16n-faderbank/16n/build/build/16n_1.jpg

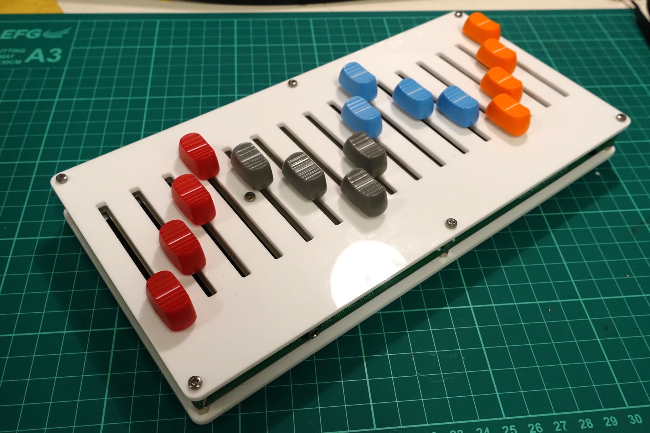
build/build/16n_1.jpg
