16n-faderbank/16n/build/build/16n_1_ics.png

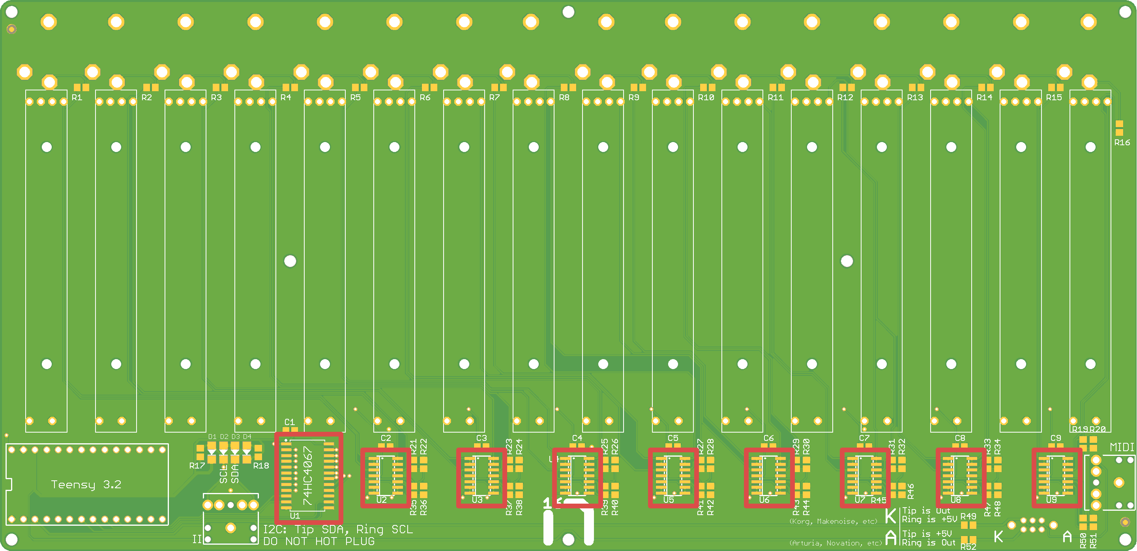
build/build/16n_1_ics.png
