16n-faderbank/16n/build/build/16n_2_rcs.png

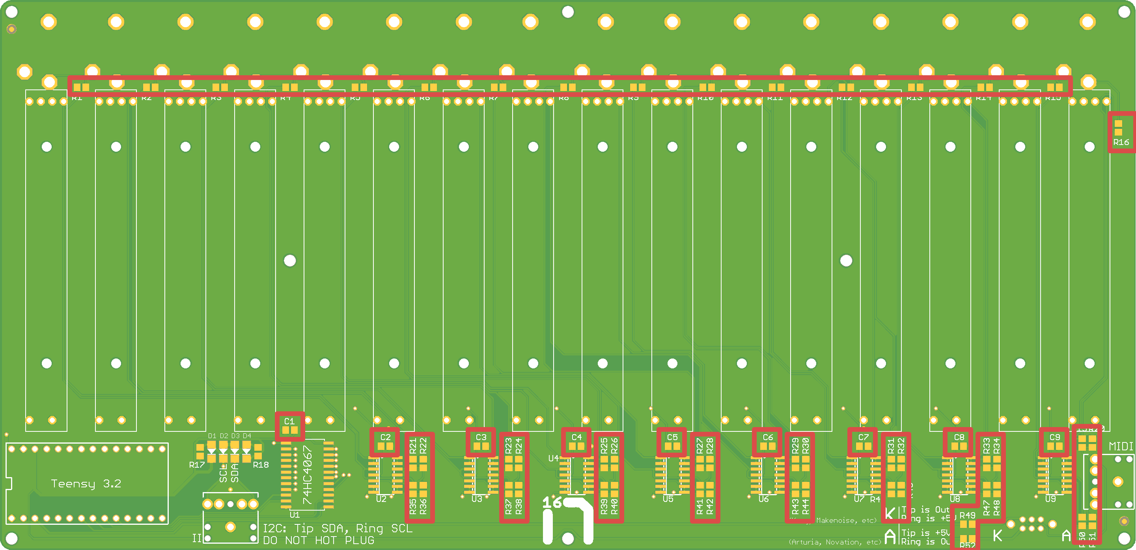
build/build/16n_2_rcs.png
