16n-faderbank/16n/build/build/16n_3.jpg

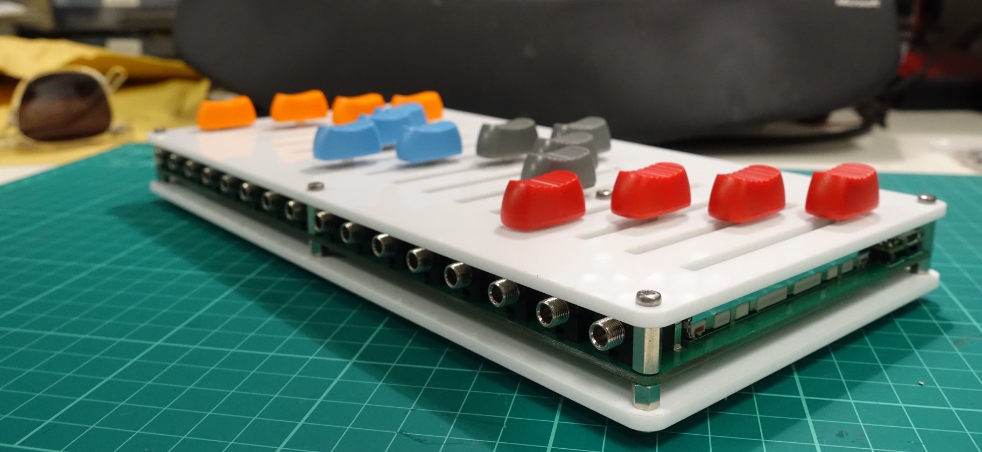
build/build/16n_3.jpg
