16n-faderbank/16n/build/build/16n_3_diodes.png

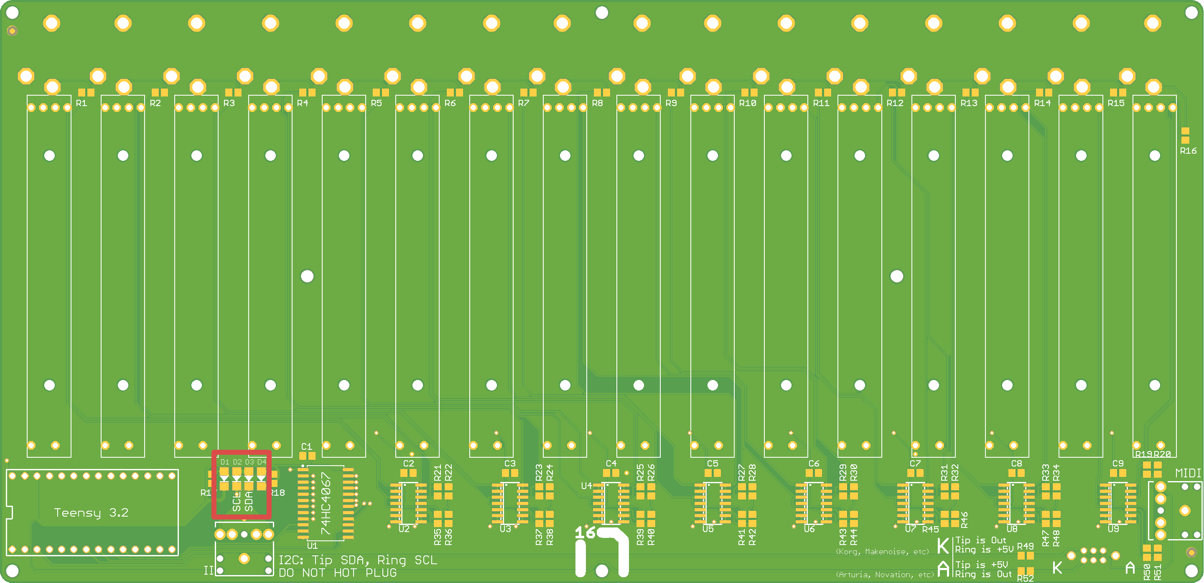
build/build/16n_3_diodes.png
