16n-faderbank/16n/build/build/16n_4_switch.png

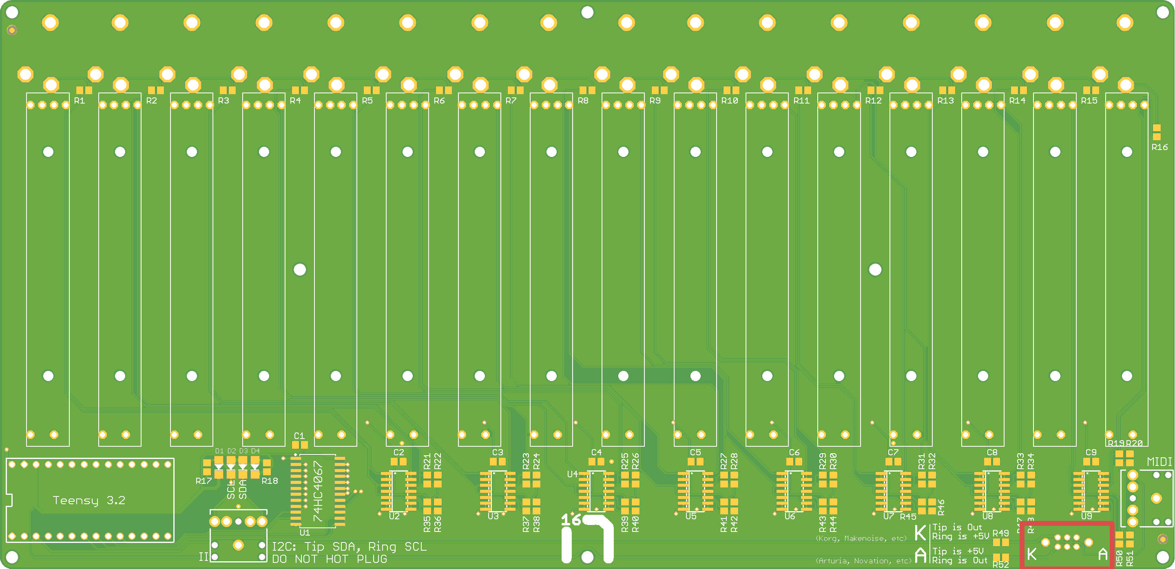
build/build/16n_4_switch.png
