16n-faderbank/16n/build/build/16n_8_faders.png

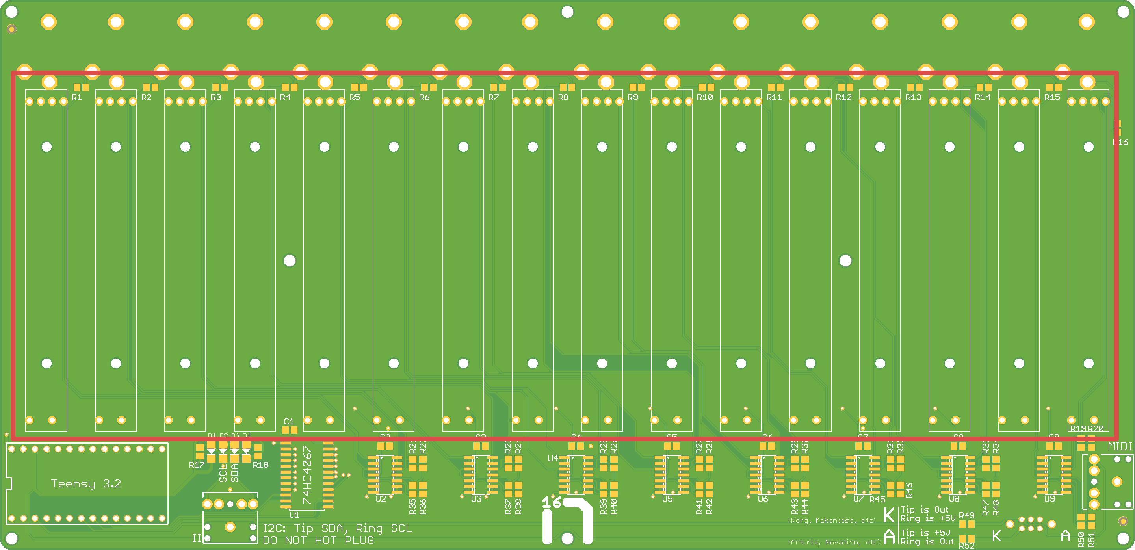
build/build/16n_8_faders.png
