16n-faderbank/16n/build/build/16n_13_labelled.png

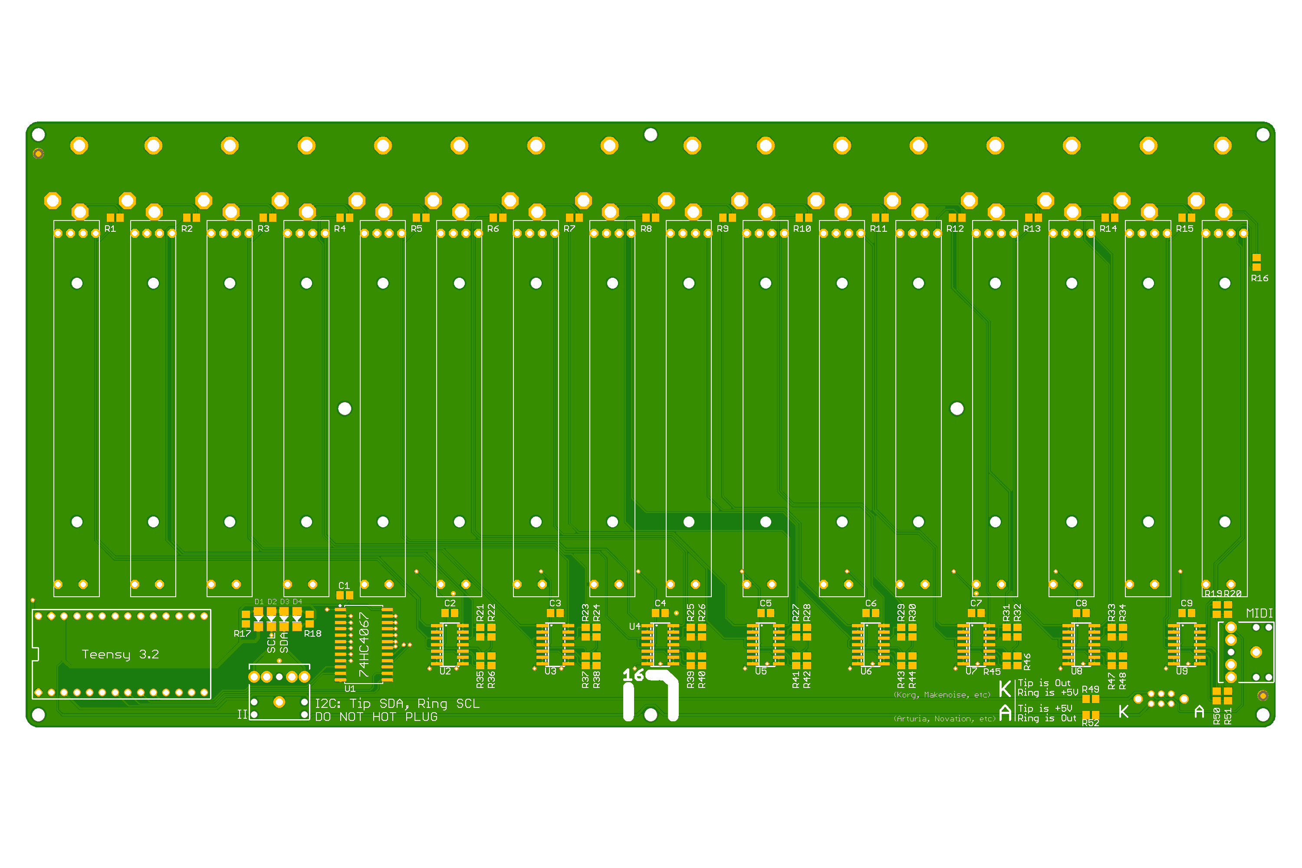
build/build/16n_13_labelled.png
