16n-faderbank/16n/build/build/16n_orientation.png

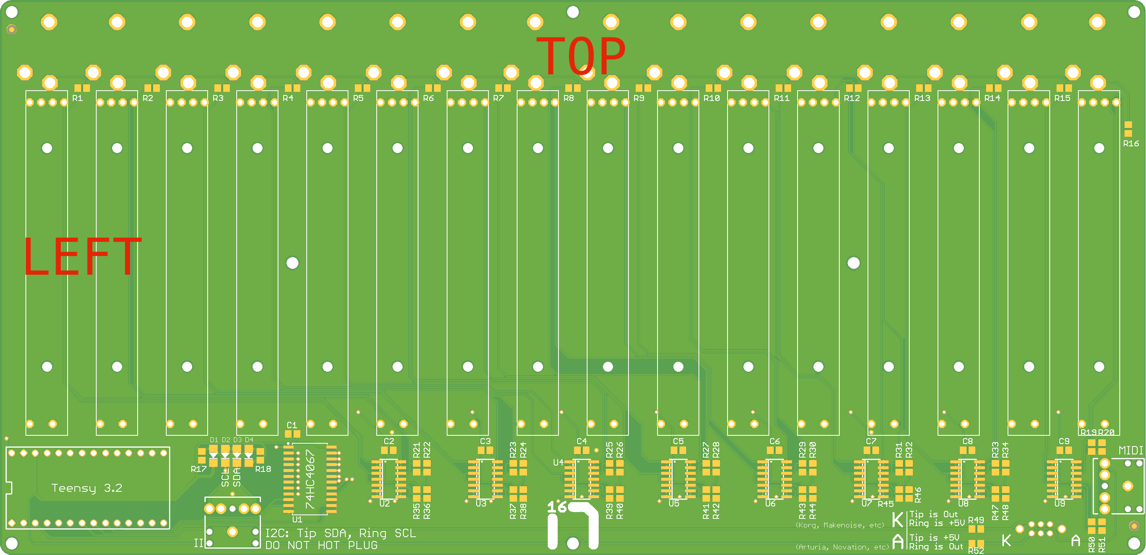
build/build/16n_orientation.png
