16n-faderbank/16n/build/build/DSC01714.JPG

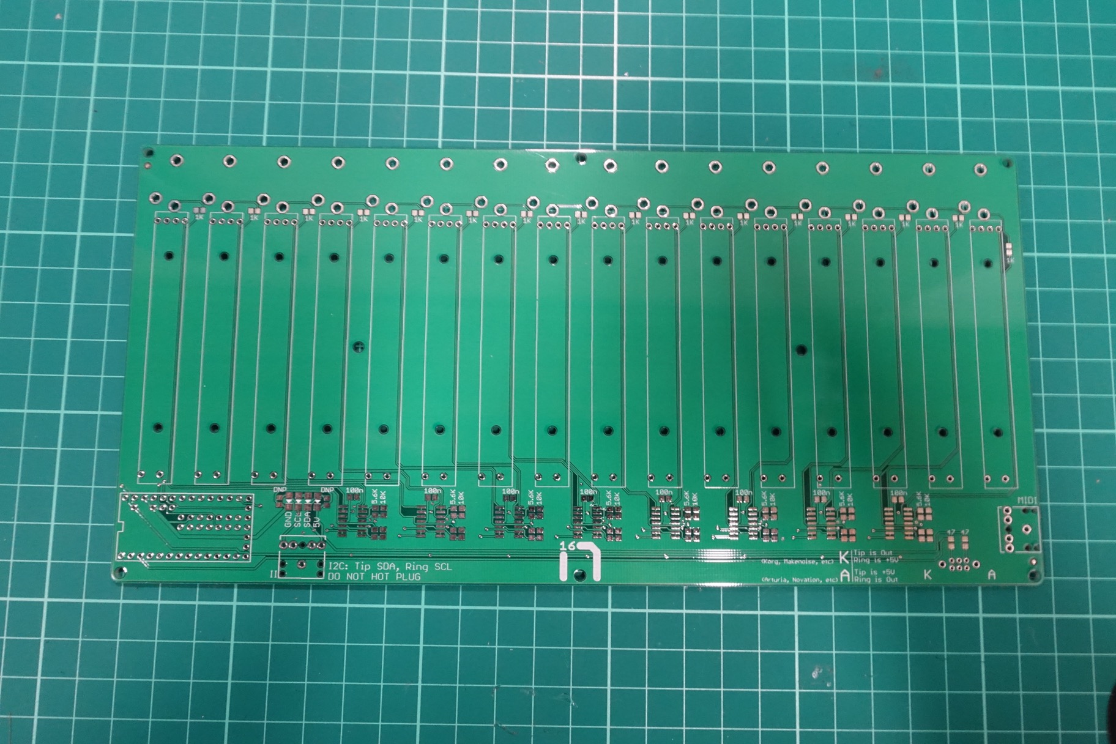
build/build/DSC01714.JPG
