16n-faderbank/16n/build/build/DSC01715.JPG

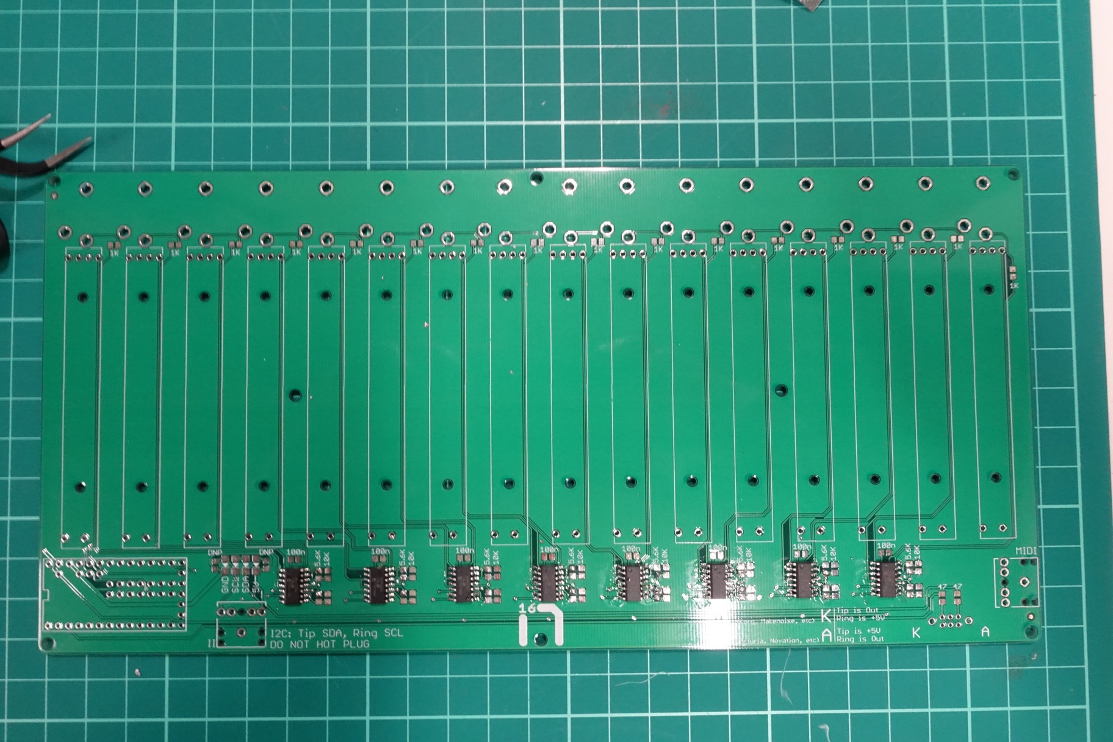
build/build/DSC01715.JPG
