16n-faderbank/16n/build/build/DSC01720.JPG

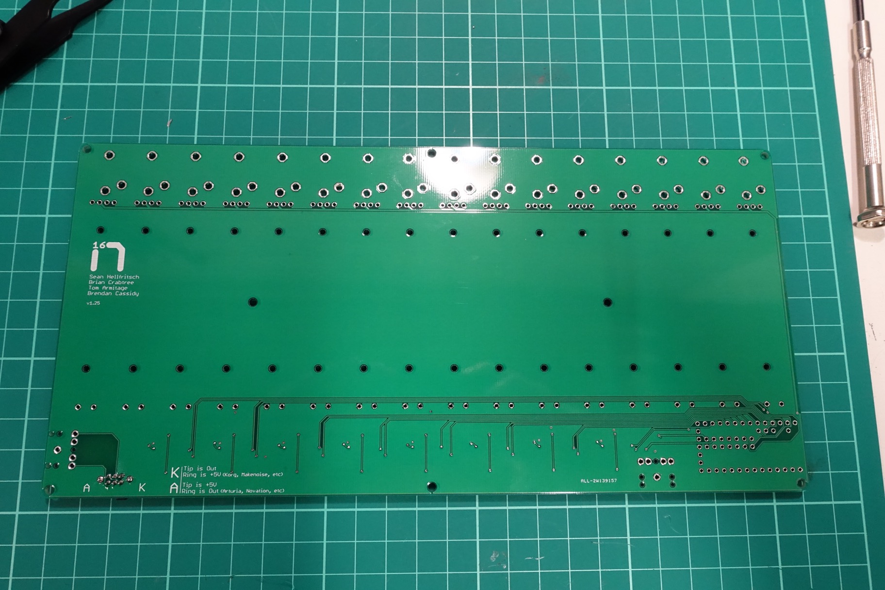
build/build/DSC01720.JPG
