16n-faderbank/16n/build/build/DSC01722.JPG

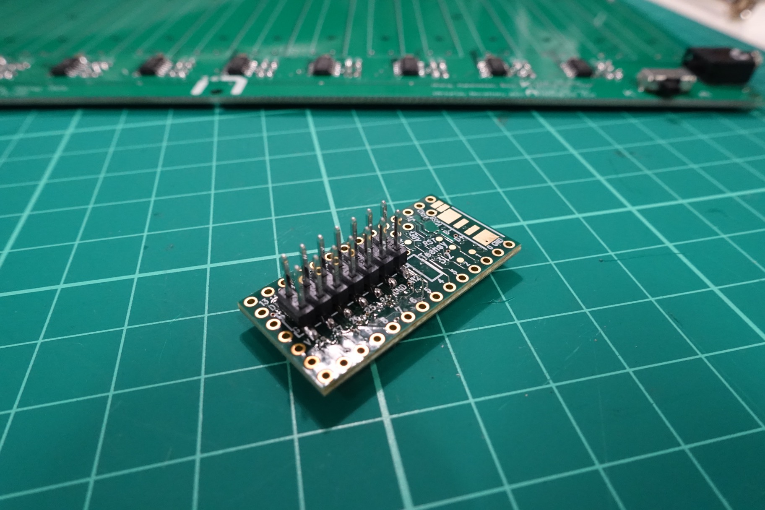
build/build/DSC01722.JPG
