16n-faderbank/16n/build/build/DSC01724.JPG

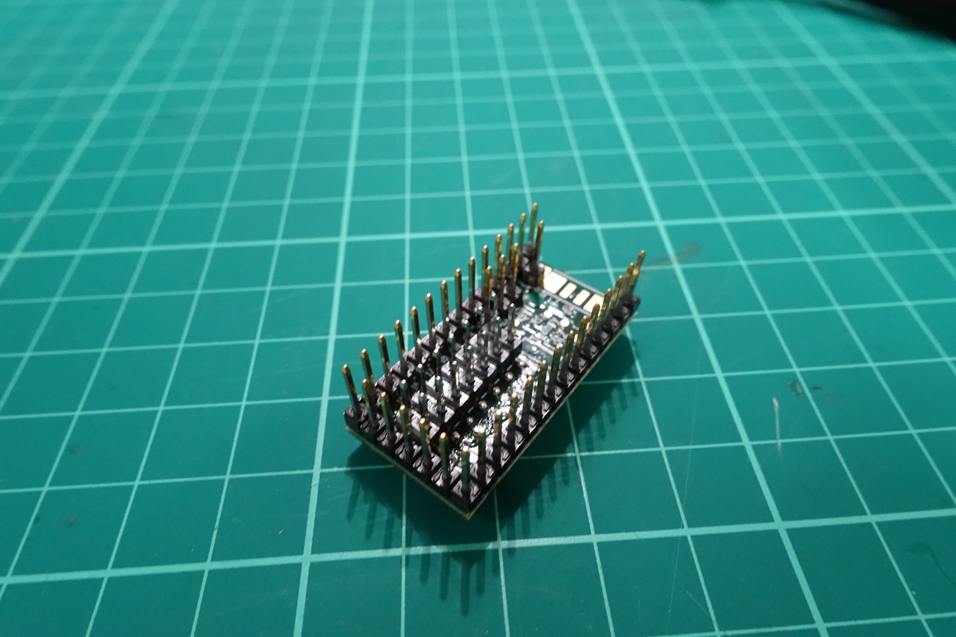
build/build/DSC01724.JPG
