16n-faderbank/16n/build/build/DSC01725.JPG

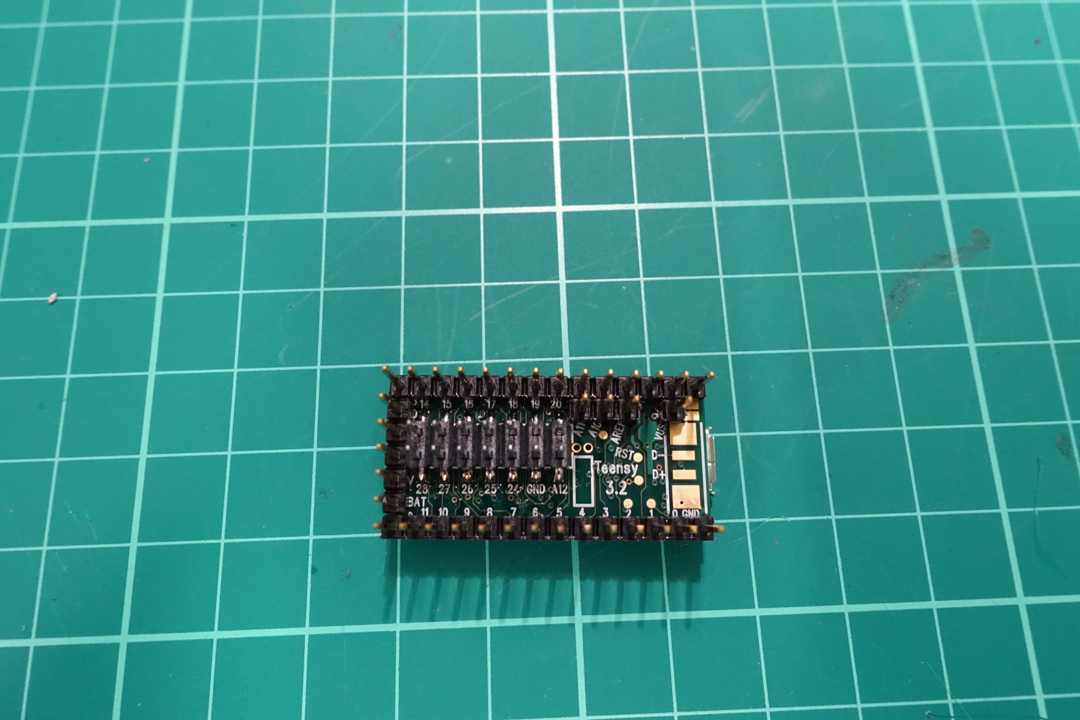
build/build/DSC01725.JPG
