16n-faderbank/16n/build/build/DSC01726.JPG

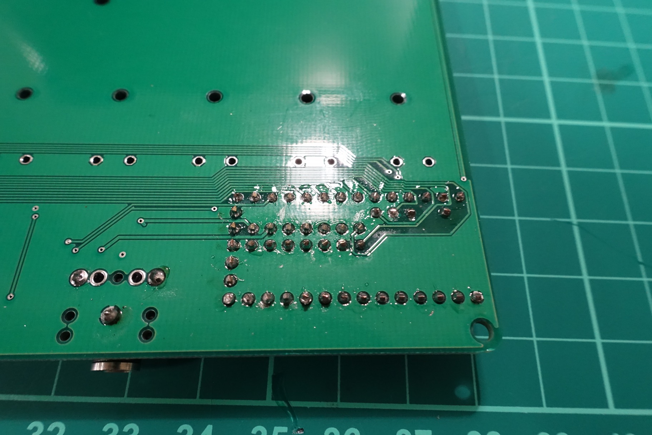
build/build/DSC01726.JPG
