16n-faderbank/16n/build/build/DSC01727.JPG

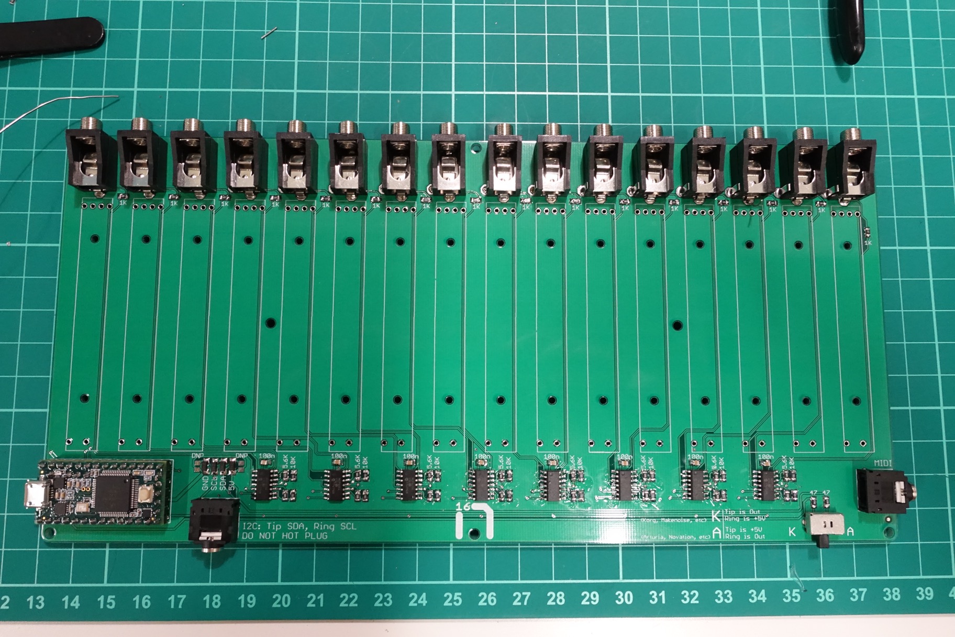
build/build/DSC01727.JPG
