16n-faderbank/16n/build/build/DSC01728.JPG

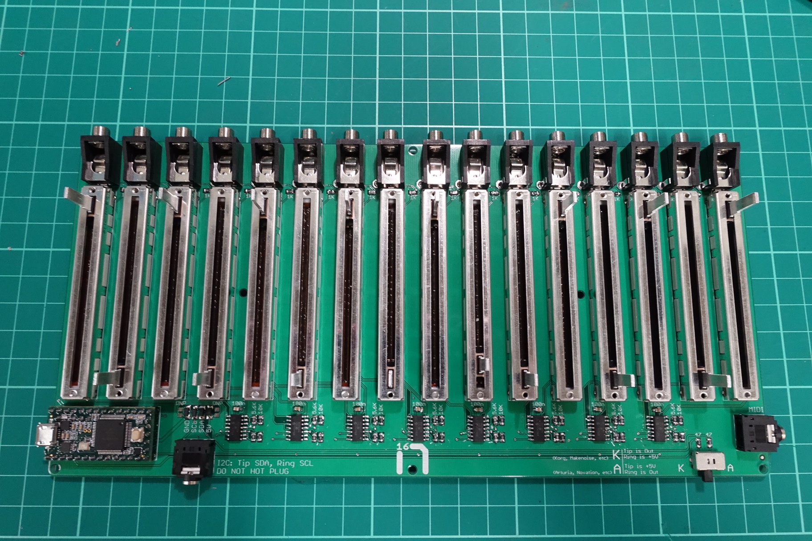
build/build/DSC01728.JPG
