16n-faderbank/16n/build/build/DSC01730.JPG

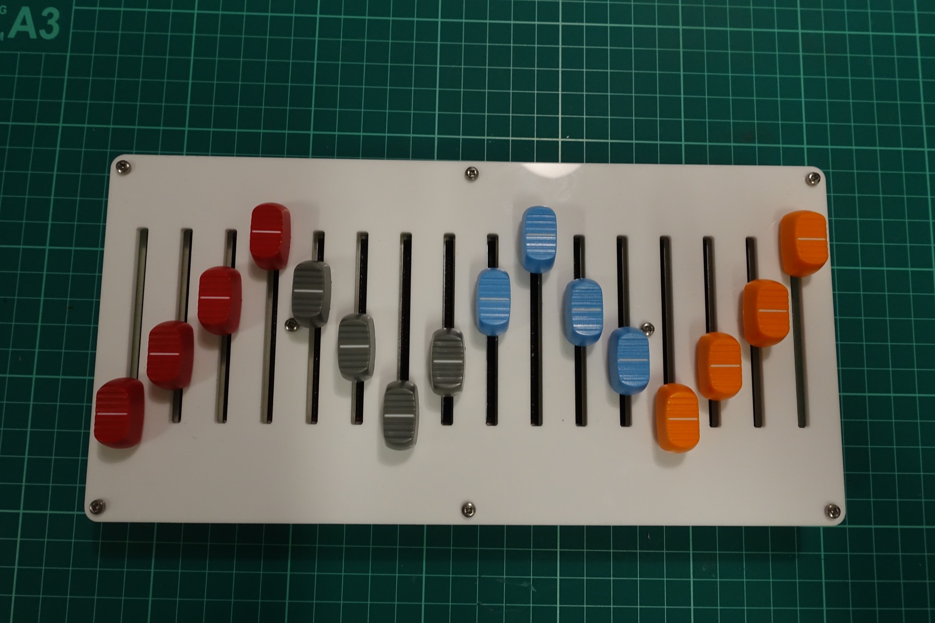
build/build/DSC01730.JPG
