16n-faderbank/16n/build/build/DSC01732.JPG

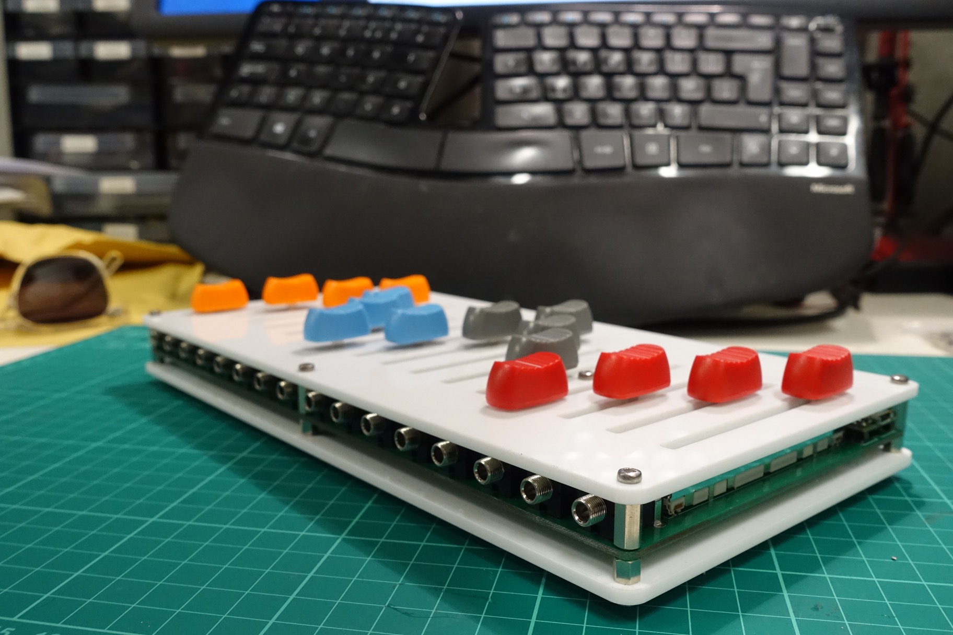
build/build/DSC01732.JPG
