16n-faderbank/16n/firmware/16n_faderbank_firmware/sysex.ino

/*
 * 16n Faderbank Configuration Sysex Processing
 * (c) 2020 by Tom Armitage
 * MIT License
 */

void processIncomingSysex(byte* sysexData, unsigned size) {
  D(Serial.println("Ooh, sysex"));
  D(printHexArray(sysexData, size));
  D(Serial.println());

  if(size < 3) {
    D(Serial.println("That's an empty sysex, bored now"));
    return;
  }

  // if(!(sysexData[1] == 0x00 && sysexData[2] == 0x58 && sysexData[3] == 0x49)) {
  if(!(sysexData[1] == 0x7d && sysexData[2] == 0x00 && sysexData[3] == 0x00)) {
    D(Serial.println("That's not a sysex message for us"));
    return;
  }

  switch(sysexData[4]) {
    case 0x1f:
      // 1F = "1nFo" - please send me your current config
      D(Serial.println("Got an 1nFo request"));
      sendCurrentState();

      // also, in 1s time, please send the current state
      // of the controls, so the editor looks nice.
      shouldSendForcedControlUpdate = true;
      sendForcedControlAt = millis() + 1000;
      break;
    case 0x0e:
      // 0E - c0nfig Edit - here is a new config
      D(Serial.println("Incoming c0nfig Edit"));
      updateAllSettingsAndStoreInEEPROM(sysexData, size);
      break;
    case 0x0d:
      // 0D - c0nfig Device edit - new config just for device opts
      D(Serial.println("Incoming c0nfig Device edit"));
      updateDeviceSettingsAndStoreInEEPROM(sysexData, size);
      break;
    case 0x0c:
      // 0C - c0nfig usb edit - here is a new config just for usb
      D(Serial.println("Incoming c0nfig usb edit"));
      updateUSBSettingsAndStoreInEEPROM(sysexData, size);
      break;
    case 0x0b:
      // 0B - c0nfig trs edit - here is a new config just for trs
      D(Serial.println("Incoming c0nfig trs edit"));
      updateTRSSettingsAndStoreInEEPROM(sysexData, size);
      break;
    case 0x1a:
      // 1A - 1nitiAlize - blank EEPROM and reset to factory settings.
      D(Serial.println("Incoming 1nitiAlize request"));
      initializeFactorySettings();
      loadSettingsFromEEPROM();
      break;
  }
}

void updateAllSettingsAndStoreInEEPROM(byte* newConfig, unsigned size) {
  // store the settings from sysex in flash
  // also update all our settings.
  D(Serial.print("Received a new config with size "));
  D(Serial.println(size));
  // D(printHexArray(newConfig,size));

  updateSettingsBlockAndStoreInEEPROM(newConfig,size,9,EEPROM_DATA_SIZE,0);
}

void updateDeviceSettingsAndStoreInEEPROM(byte* newConfig, unsigned size) {
  // store the settings from sysex in flash
  // also update all our settings.
  D(Serial.print("Received a new device config with size "));
  D(Serial.println(size));
  // D(printHexArray(newConfig,size));

  updateSettingsBlockAndStoreInEEPROM(newConfig,size,5,16,0);
}

void updateUSBSettingsAndStoreInEEPROM(byte* newConfig, unsigned size) {
  // store channels
  updateSettingsBlockAndStoreInEEPROM(newConfig,size,5,16,16);
  // store CCs
  updateSettingsBlockAndStoreInEEPROM(newConfig,size,21,16,48);
  // store 14-bit flags
  updateSettingsBlockAndStoreInEEPROM(newConfig,size,37,3,80);
}

void updateTRSSettingsAndStoreInEEPROM(byte* newConfig, unsigned size) {
  // store channels
  updateSettingsBlockAndStoreInEEPROM(newConfig,size,5,16,32);
  // store CCs
  updateSettingsBlockAndStoreInEEPROM(newConfig,size,21,16,64);
  // store 14-bit flags
  updateSettingsBlockAndStoreInEEPROM(newConfig,size,37,3,83);
}

void updateSettingsBlockAndStoreInEEPROM(byte* configFromSysex, unsigned sysexSize, int configStartIndex, int configDataLength, int EEPROMStartIndex) { 
  D(Serial.print("Storing data of size "));
  D(Serial.print(configDataLength));
  D(Serial.print(" at location "));
  D(Serial.print(EEPROMStartIndex));
  D(Serial.print(" from data of length "));
  D(Serial.print(sysexSize));
  D(Serial.print(" beginning at byte "));
  D(Serial.println(configStartIndex));
  D(printHexArray(configFromSysex, sysexSize));

  // walk the config, ignoring the top, tail, and firmware version
  byte dataToWrite[configDataLength];
  unsigned dataToWriteLength = configDataLength;

  for(int i = 0; i < (configDataLength); i++) {
    unsigned configIndex = i + configStartIndex;
    if (configIndex >= sysexSize) {
      // the sysex message is shorter than expected, only write what we receieved
      dataToWriteLength = i;
      break;
    }
    dataToWrite[i] = configFromSysex[configIndex];
  }

  // write new Data
  writeEEPROMArray(EEPROMStartIndex, dataToWrite, dataToWriteLength);

  // now load that.
  loadSettingsFromEEPROM();
}
void sendCurrentState() {
  //   0F - "c0nFig" - outputs its config:
  byte sysexData[EEPROM_DATA_SIZE + 8];

  sysexData[0] = 0x7d; // manufacturer
  sysexData[1] = 0x00;
  sysexData[2] = 0x00;
  
  sysexData[3] = 0x0F; // ConFig;

  sysexData[4] = DEVICE_ID; // Device 01, ie, dev board
  sysexData[5] = MAJOR_VERSION; // major version
  sysexData[6] = MINOR_VERSION; // minor version
  sysexData[7] = POINT_VERSION; // point version
  

  // 	16 bytes of config flags, notably:
  // 	LED PERMANENT
  // 	LED DATA XFER
  // 	ROTATE (flip+reverse)
  //  i2c MASTER/FOLLOEWR
  //  fadermin LSB
  //  fadermin MSB
  //  fadermax LSB
  //  fadermax MSB
  //  Soft MIDI thru

  // 	16x USBccs
  // 	16x TRSccs
  // 	16x USBchannel
  // 	16x TRS channel
  //  3 bytes for USB CC modes
  //  3 bytes for TRS CC modes
    
  // So that's 3 for the mfg + 1 for the message + 86 bytes
  // can be done with a simple "read EEPROM_DATA_SIZE bytes and send them."

  byte buffer[EEPROM_DATA_SIZE];
  readEEPROMArray(0, buffer, EEPROM_DATA_SIZE);

  int offset = 8;
  for(int i = 0; i < EEPROM_DATA_SIZE; i++) {
    byte data = buffer[i] & 0x7F;
    sysexData[i+offset] = data;
  }

  D(Serial.println("Sending this data"));
  D(printHexArray(sysexData, EEPROM_DATA_SIZE + 8));

  usbMIDI.sendSysEx(EEPROM_DATA_SIZE + 8, sysexData, false);
  forceMidiWrite = true;
}
